hemonserrat/jadeku/img/ADQ-2.JPG

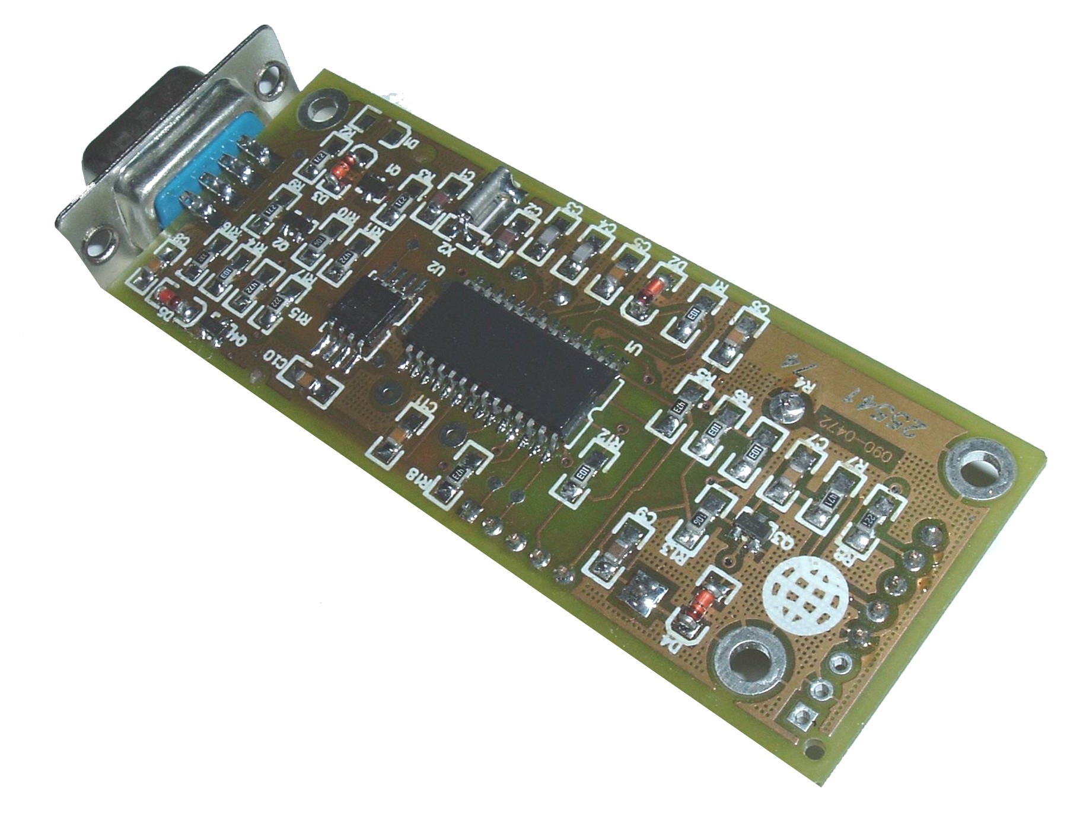
img/ADQ-2.JPG
